lucansky/hexamon/boards/busunit/board_image.png

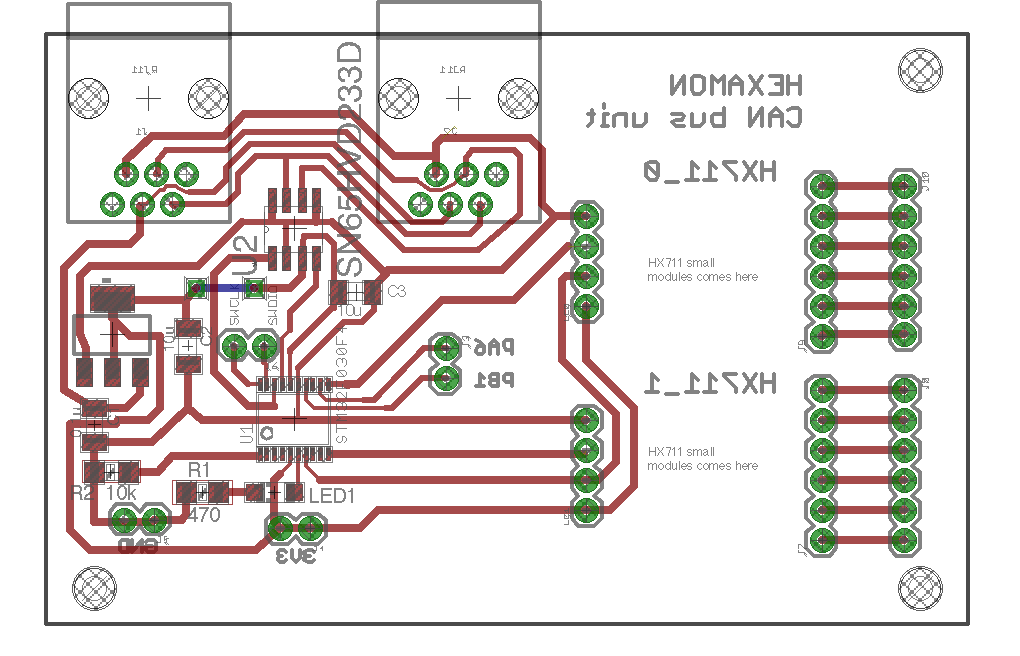
boards/busunit/board_image.png
