lucansky/hexamon/boards/master_can_shield/schema_image.png

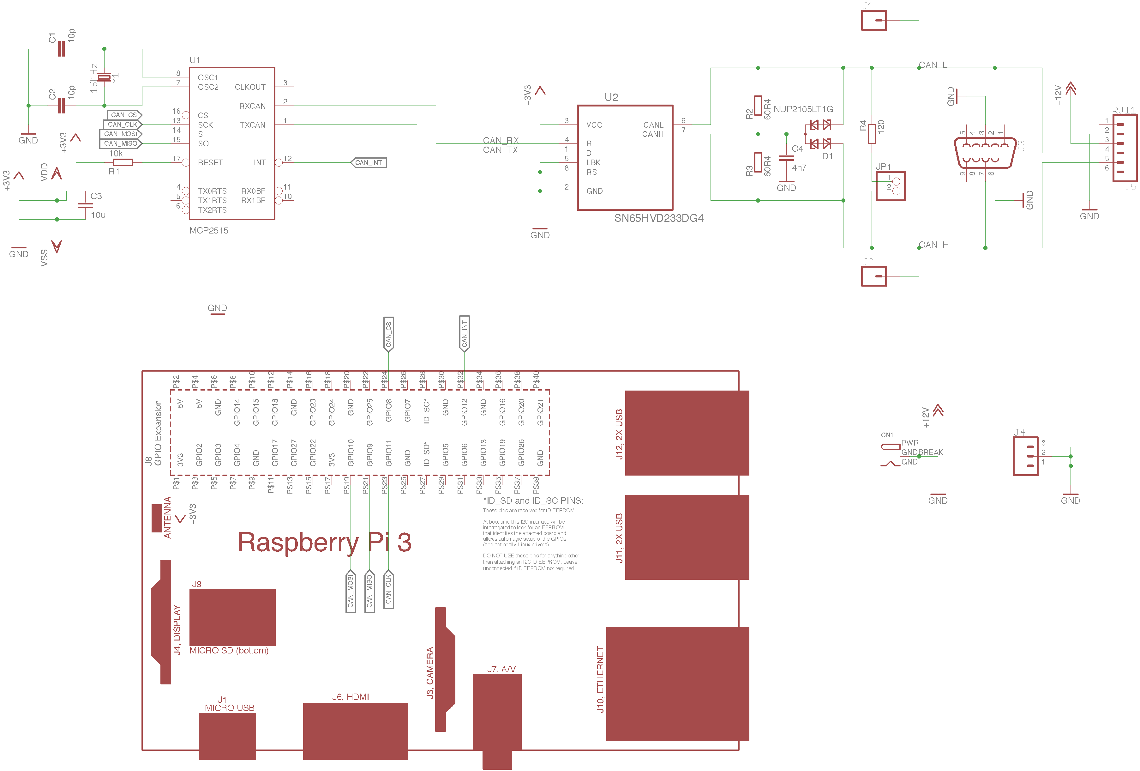
boards/master_can_shield/schema_image.png
