lucansky/hexamon/boards/power_board/board_image.png

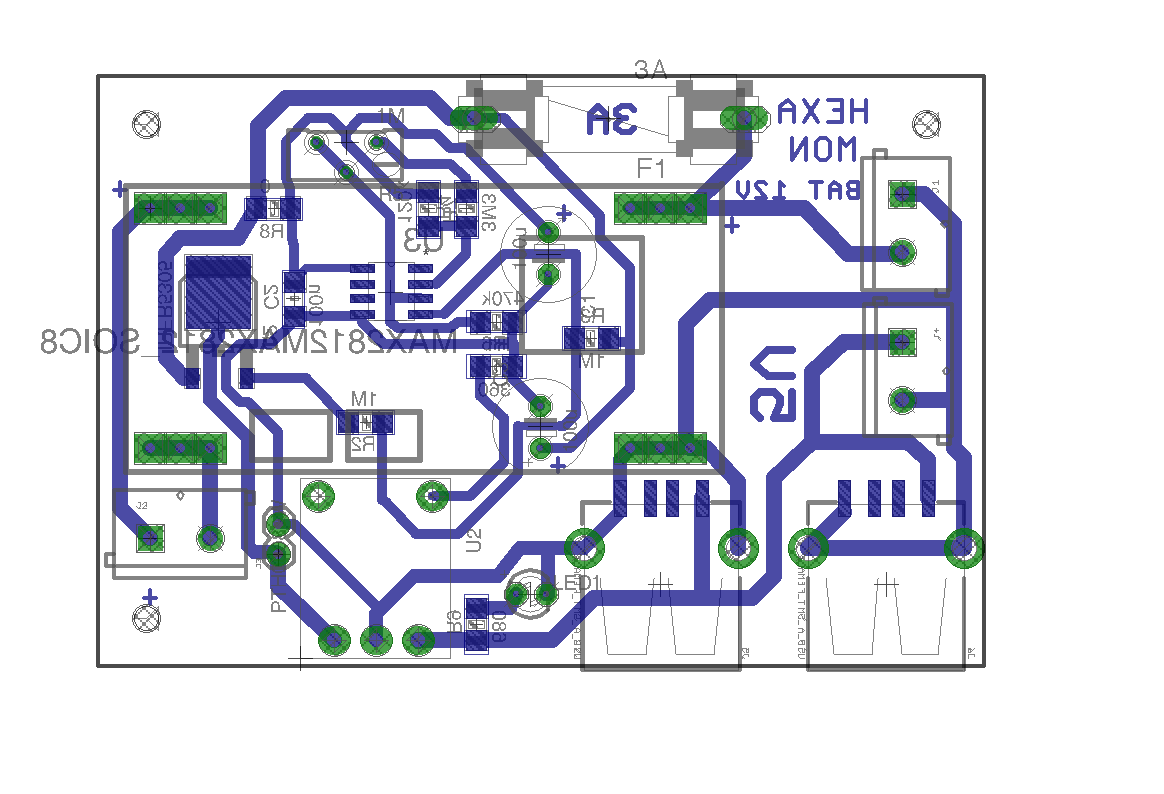
boards/power_board/board_image.png
